XEMACS-666/TriBit-Lux/Version_1.1/pcb/PCB_PCB_TriBitLux_V1_1-LIC_2_2026-10-06/Multi-Layer.pdf

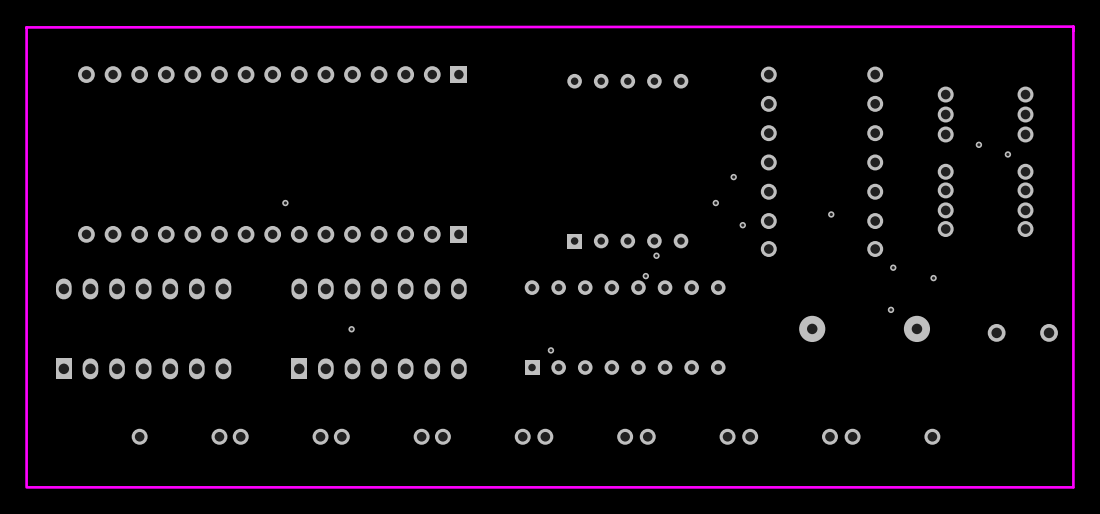
[picture p29: page 1]
